MatthewChamot/LEDAnalogClock/Clock CAD/LED.SLDPRT

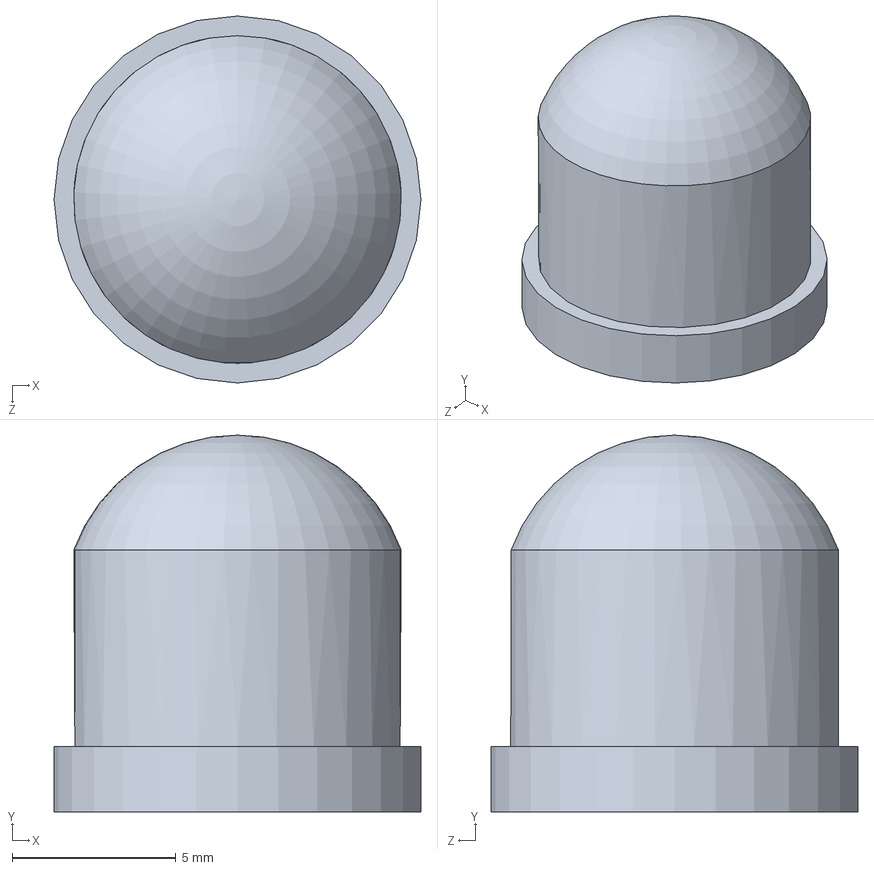
[picture p16: CAD file, 2018-05-07]
Clock CAD/LED.SLDPRT
11.2 x 11.5 x 11.2 mm
