MatthewChamot/LEDAnalogClock/Clock CAD/Peg.SLDPRT

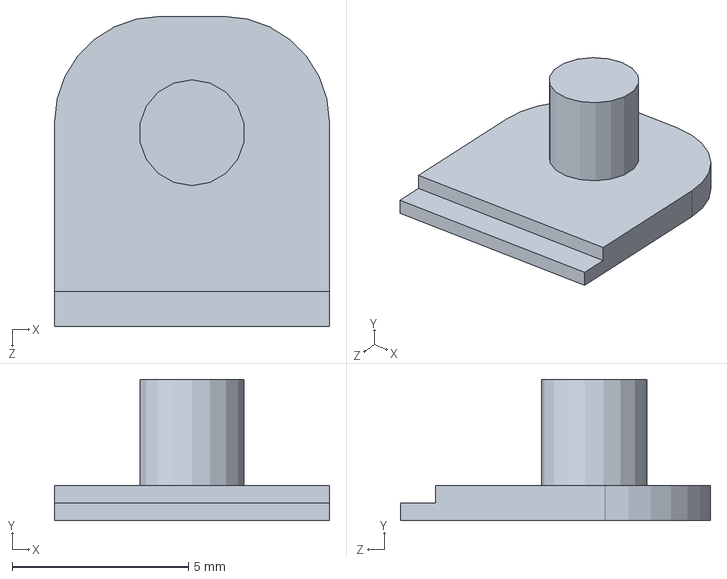
[picture p17: CAD file, 2018-05-07]
Clock CAD/Peg.SLDPRT
7.80 x 4.00 x 8.80 mm
