MatthewChamot/LEDAnalogClock/Clock CAD/Light.SLDPRT

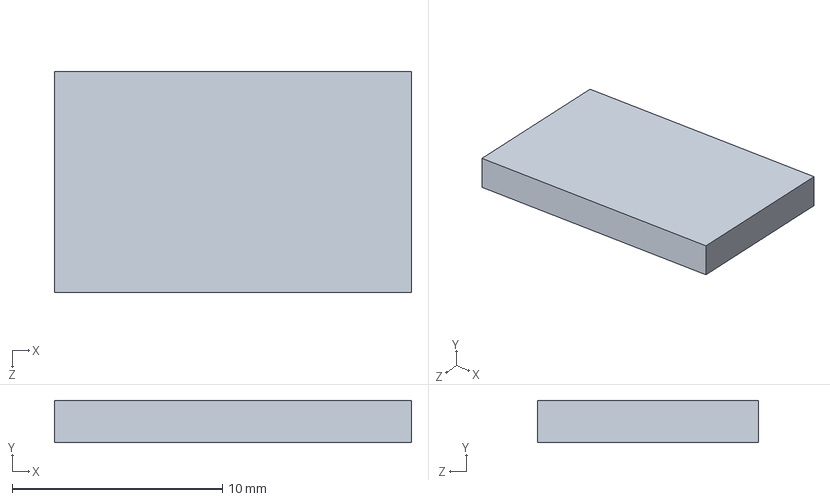
[picture p18: CAD file, 2018-05-07]
Clock CAD/Light.SLDPRT
17.0 x 2.00 x 10.5 mm
