MatthewChamot/LEDAnalogClock/Clock CAD/QuadHorn.SLDPRT

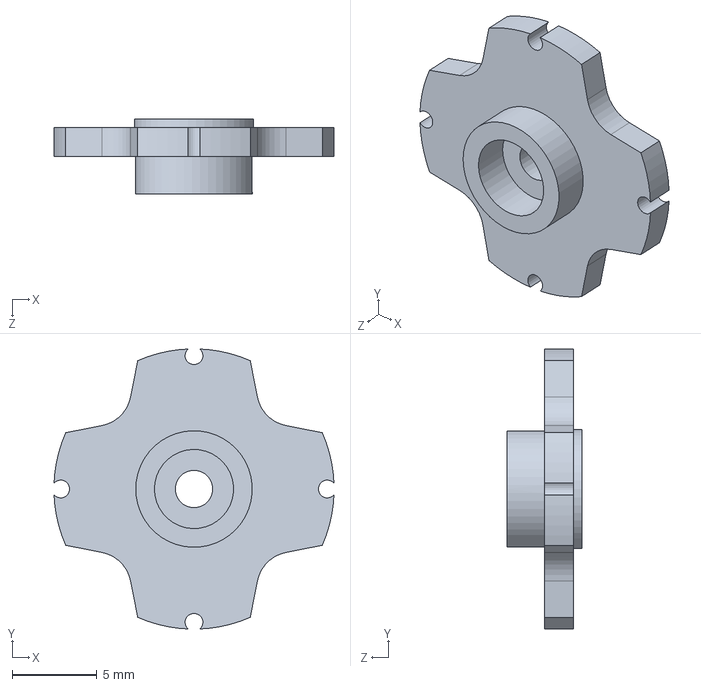
[picture p19: CAD file, 2018-05-07]
Clock CAD/QuadHorn.SLDPRT
16.5 x 16.5 x 4.42 mm
