MatthewChamot/LEDAnalogClock/Clock CAD/Test.STL

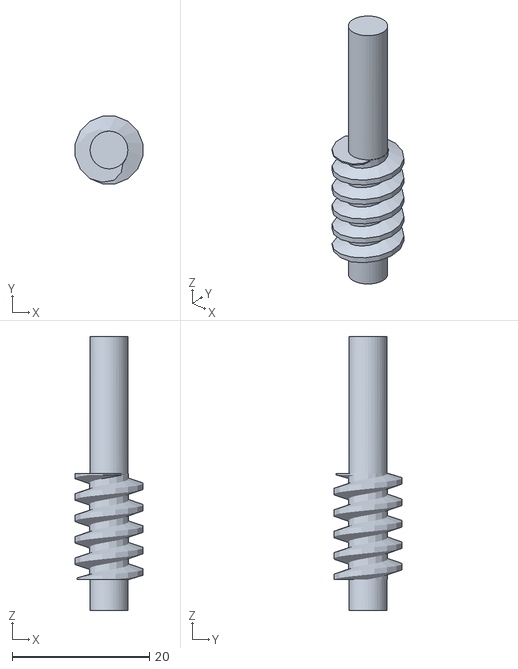
[picture p20: CAD file, 2018-05-07]
Clock CAD/Test.STL
9.86 x 9.85 x 40.0
