MatthewChamot/LEDAnalogClock/Clock CAD/Body.SLDPRT

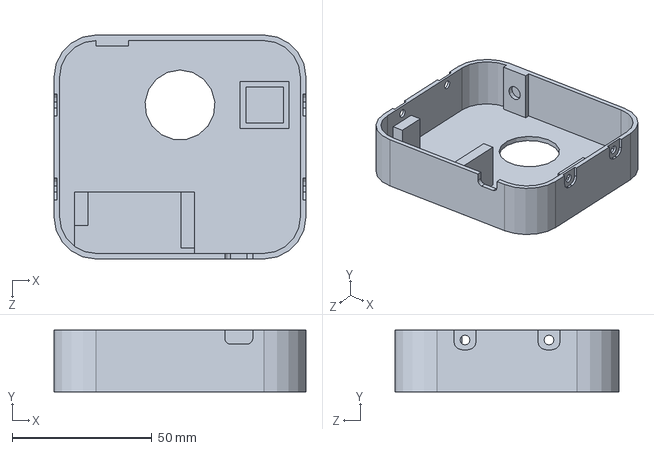
[picture p21: CAD file, 2018-05-07]
Clock CAD/Body.SLDPRT
90.0 x 22.0 x 80.0 mm
