MatthewChamot/LEDAnalogClock/Clock CAD/Arm3.SLDPRT

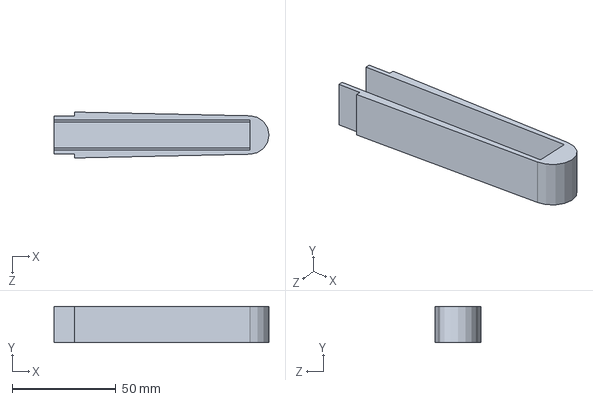
[picture p22: CAD file, 2018-05-07]
Clock CAD/Arm3.SLDPRT
103.6 x 17.5 x 22.1 mm
