MatthewChamot/LEDAnalogClock/Clock CAD/Micro Servo.SLDPRT

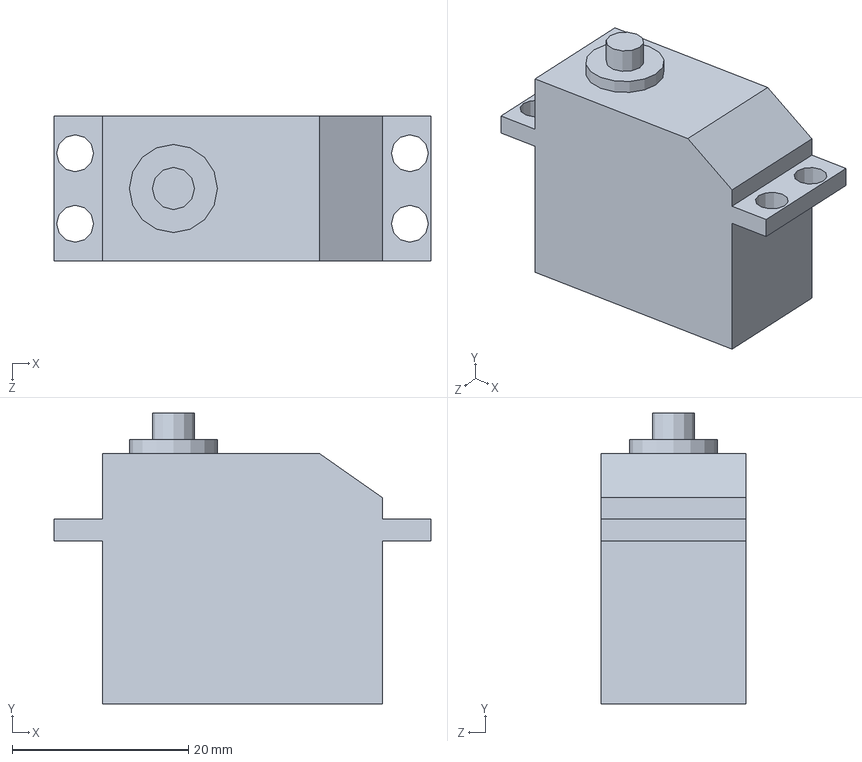
[picture p23: CAD file, 2018-05-07]
Clock CAD/Micro Servo.SLDPRT
42.8 x 33.0 x 16.5 mm
