MatthewChamot/LEDAnalogClock/Clock CAD/Teensy32.SLDPRT

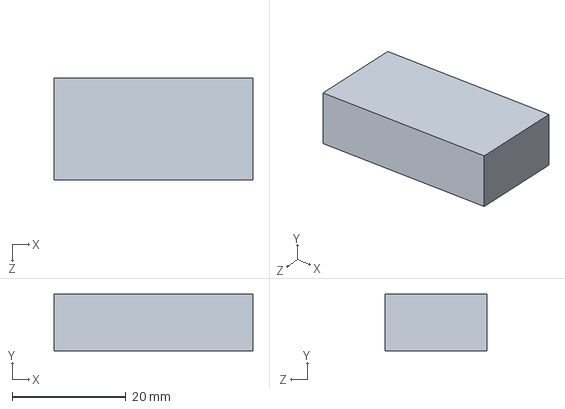
[picture p24: CAD file, 2018-05-07]
Clock CAD/Teensy32.SLDPRT
35.0 x 10.0 x 18.0 mm
